shannon-greenlight/Thors-Arsenal/main_board/hardware.kicad_sch

## KiCad design main_board/hardware.kicad_sch (2025-01-23)

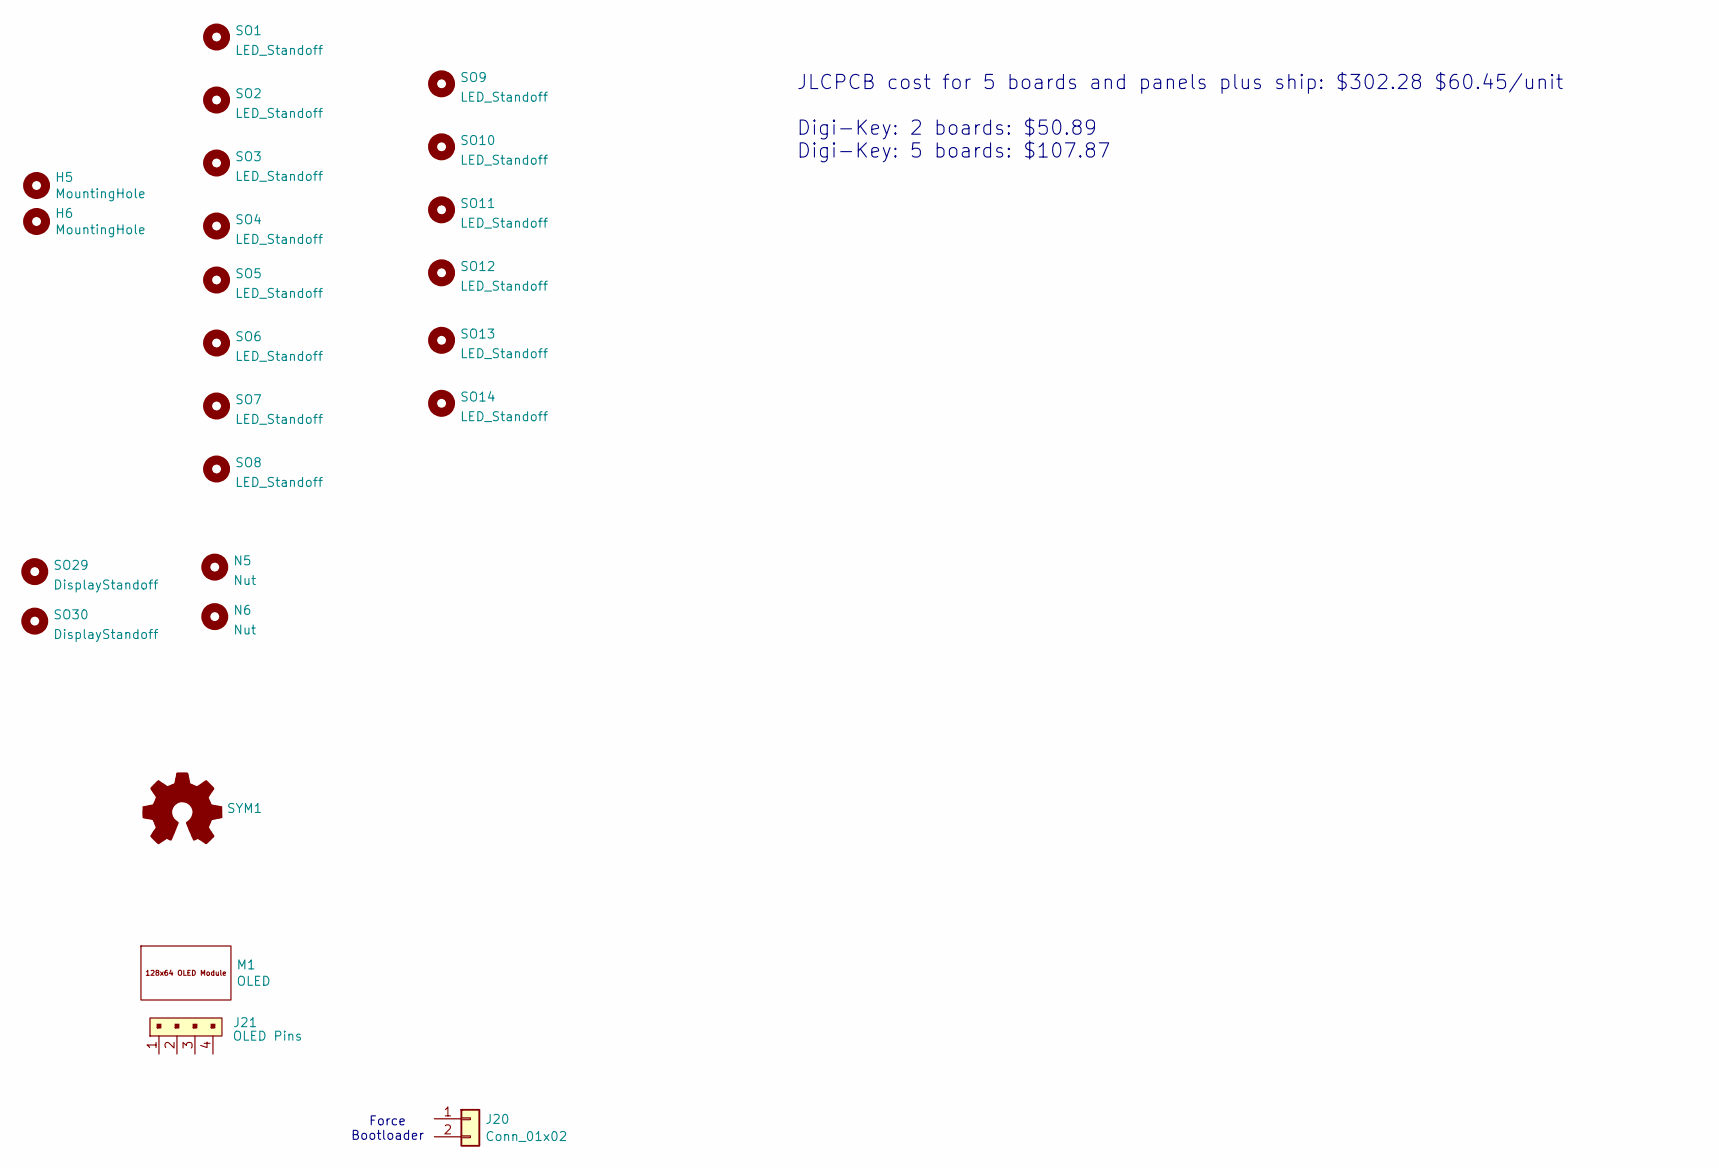
[picture p18: schematic hardware.kicad_sch]

Parts:
H5, H6: MountingHole; MountingHole_2.5mm-No-Margin
J20: Conn_01x02; Digi-Key Part 609-2997-ND
J21: OLED Pins; Digi-Key Part MTLW-104-05-G-S-170-ND
M1: OLED
N5, N6: Nut; Digi-Key Part 36-4687-ND
SO1, SO2, SO3, SO4, SO5, SO6, SO7, SO8, SO9, SO10, SO11, SO12, SO13, SO14: LED_Standoff; Digi-Key Part 732-11594-ND
SO29, SO30: DisplayStandoff; Digi-Key Part 732-13045-ND
SYM1: Logo_Open_Hardware_Small; OSHW-Logo2_7.3x6mm_SilkScreen

Notes on the sheet:
JLCPCB cost for 5 boards and panels plus ship: $302.28 $60.45/unit Digi-Key: 2 boards: $50.89 Digi-Key: 5 boards: $107.87
Force Bootloader
