shannon-greenlight/Thors-Arsenal/main_board/inputs.kicad_sch

## KiCad design main_board/inputs.kicad_sch (2025-01-23)

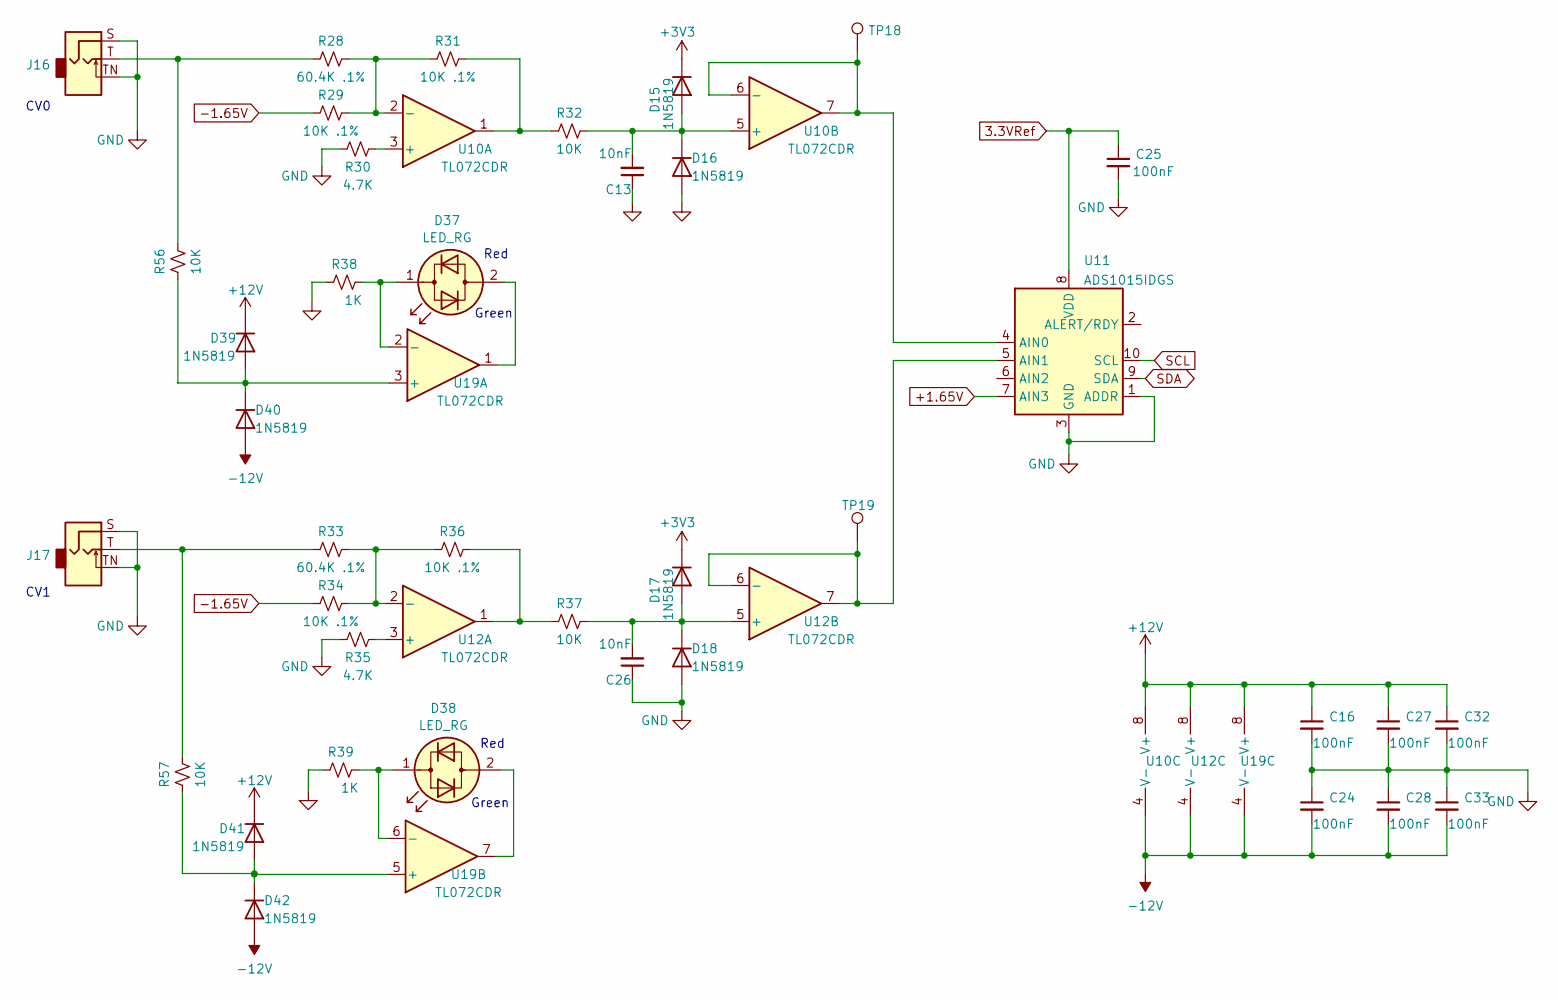
[picture p19: schematic inputs.kicad_sch]

Parts:
C13, C26: 10nF; C_0805_2012Metric_Pad1.18x1.45mm_HandSolder; Digi-Key Part 311-1136-1-ND
C16, C24, C25, C27, C28, C32, C33: 100nF; C_0603_1608Metric; Digi-Key Part 478-10836-1-ND
D15, D16, D17, D18, D39, D40, D41, D42: 1N5819; D_SOD-323; Digi-Key Part 478-7800-1-ND
D37, D38: LED_RG; LED_D3.0mm; Digi-Key Part 754-WP937SURKCGKW-ND
J16, J17: 3.5mm Jack; Jack_3.5mm_QingPu_WQP-PJ398SM_Vertical
R28, R33: 60.4K .1%; R_0603_1608Metric; Digi-Key Part P30.1KDACT-ND
R29, R31, R34, R36: 10K .1%; R_0805_2012Metric_Pad1.20x1.40mm_HandSolder; Digi-Key Part P10KDACT-ND
R30, R35: 4.7K; R_0805_2012Metric_Pad1.20x1.40mm_HandSolder; Digi-Key Part RMCF0805FT4K70CT-ND
R32, R37, R56, R57: 10K; R_0805_2012Metric_Pad1.20x1.40mm_HandSolder; Digi-Key Part 13-RC0805JR-1010KLCT-ND
R38, R39: 1K; R_0805_2012Metric_Pad1.20x1.40mm_HandSolder; Digi-Key Part RNCP0805FTD1K00CT-ND
TP18, TP19: TestPoint; TestPoint_Keystone_5000-5004_Miniature; Digi-Key Part 36-5006-ND
U10, U12, U19: TL072CDR; SOIC-8_3.9x4.9mm_P1.27mm; Digi-Key Part 296-1282-1-ND
U11: ADS1015IDGS; TSSOP-10_3x3mm_P0.5mm; LCSC Part # C193969

Connections:
3.3VRef: C25.1, U11.8 (VDD)
+1.65V: U11.7 (AIN3)
+3V3: D15.1 (K), D17.1 (K)
+12V: C16.1, C27.1, C32.1, D39.1 (K), D41.1 (K), U10.8 (V+), U12.8 (V+), U19.8 (V+)
-1.65V: R29.2, R34.2
-12V: C24.2, C28.2, C33.2, D40.2 (A), D42.2 (A), U10.4 (V-), U12.4 (V-), U19.4 (V-)
GND: C13.1, C16.2, C24.1, C25.2, C26.1, C27.2, C28.1, C32.2, C33.1, D16.2 (A), D18.2 (A), J16.S, J16.TN, J17.S, J17.TN, R30.2, R35.2, R38.1, R39.1, U11.1 (ADDR), U11.3 (GND)
unnamed: C13.2, D15.2 (A), D16.1 (K), R32.1, U10.5 (+)
unnamed: C26.2, D17.2 (A), D18.1 (K), R37.1, U12.5 (+)
unnamed: D37.1 (KA), R38.2, U19.2 (-)
unnamed: D37.2 (AK), U19.1
unnamed: D38.1 (KA), R39.2, U19.6 (-)
unnamed: D38.2 (AK), U19.7
unnamed: D39.2 (A), D40.1 (K), R56.2, U19.3 (+)
unnamed: D41.2 (A), D42.1 (K), R57.2, U19.5 (+)
unnamed: J16.T, R28.2, R56.1
unnamed: J17.T, R33.2, R57.1
unnamed: R28.1, R29.1, R31.2, U10.2 (-)
unnamed: R30.1, U10.3 (+)
unnamed: R31.1, R32.2, U10.1
unnamed: R33.1, R34.1, R36.2, U12.2 (-)
unnamed: R35.1, U12.3 (+)
unnamed: R36.1, R37.2, U12.1
unnamed: TP18.1, U10.6 (-), U10.7, U11.4 (AIN0)
unnamed: TP19.1, U11.5 (AIN1), U12.6 (-), U12.7
SCL: U11.10 (SCL)
SDA: U11.9 (SDA)

Notes on the sheet:
CV0
Red
CV1
Green
