shannon-greenlight/Thors-Arsenal/main_board/main_board.kicad_sch

## KiCad design main_board/main_board.kicad_sch (2025-01-23)

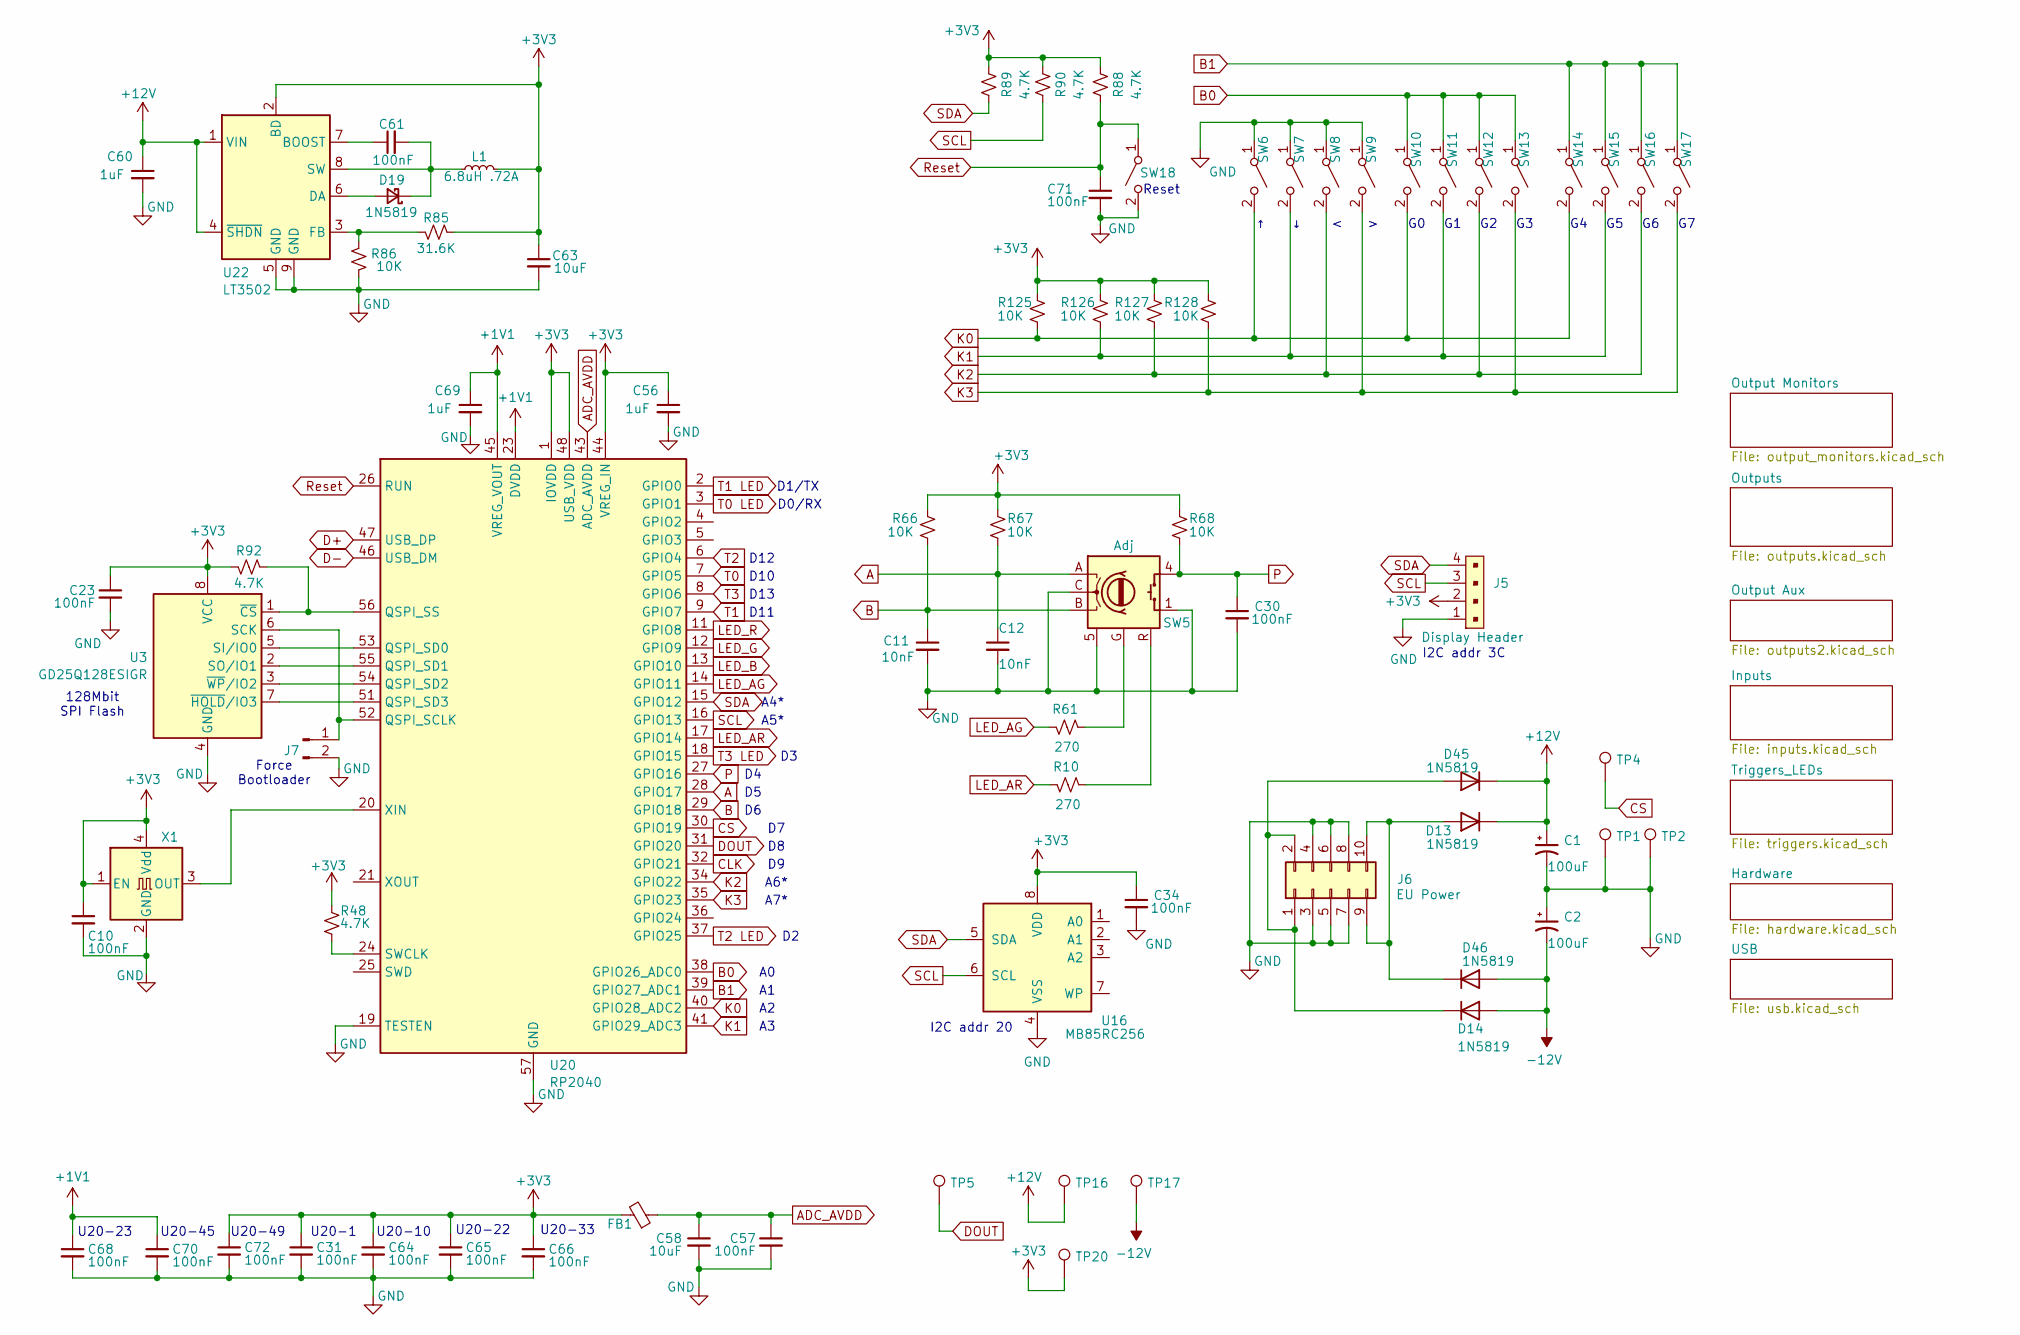
[picture p20: schematic main_board.kicad_sch]

Parts:
C1, C2: 100uF; CP_Elec_6.3x5.4_Nichicon; Digi-Key Part 399-A768EB107M1ELAE036DKR-ND
C10, C23, C30, C31, C34, C57, C61, C64, C65, C66, C68, C70, C71, C72: 100nF; C_0603_1608Metric; Digi-Key Part 478-10836-1-ND
C11, C12: 10nF; C_0805_2012Metric_Pad1.18x1.45mm_HandSolder; Digi-Key Part 311-1136-1-ND
C56, C69: 1uF; C_0603_1608Metric; Digi-Key Part 1276-1029-1-ND
C58, C63: 10uF; C_0603_1608Metric; Digi-Key Part 1276-1029-1-ND
C60: 1uF; C_0805_2012Metric_Pad1.18x1.45mm_HandSolder; Digi-Key Part 1276-1029-1-ND
D13, D14, D19, D45, D46: 1N5819; D_SOD-323; Digi-Key Part 478-7800-1-ND
FB1: BLM18PG471SN1D; L_Murata_BLM18P; LCSC Part # C1002
J5: Display Header; OLED_Header_Slim; MPN 0022232041; Digi-Key Part SAM1087-04-ND
J6: EU Power; PinHeader_2x05_P2.54mm_Vertical; Digi-Key Part S2011EC-05-ND
J7: Conn_01x02_Male; PinHeader_1x02_P2.54mm_Vertical; Digi-Key Part 609-4938-ND
L1: 6.8uH .72A; L_1812_4532Metric; LCSC Part # C703769
R10, R61: 270; R_0603_1608Metric; Digi-Key Part RMCF0603FT23K7CT-ND
R48: 4.7K; R_0603_1608Metric; Digi-Key Part RMCF0805FT4K70CT-ND
R66, R67: 10K; R_0402_1005Metric; Digi-Key Part 13-RC0805JR-1010KLCT-ND
R68, R125, R126, R127, R128: 10K; R_0805_2012Metric_Pad1.20x1.40mm_HandSolder; Digi-Key Part 13-RC0805JR-1010KLCT-ND
R85: 31.6K; R_0603_1608Metric; Digi-Key Part RMCF0603FT23K7CT-ND
R86: 10K; R_0402_1005Metric; Digi-Key Part RMCF0603FT23K7CT-ND
R88, R89, R90, R92: 4.7K; R_0805_2012Metric_Pad1.20x1.40mm_HandSolder; Digi-Key Part RMCF0805FT4K70CT-ND
SW5: Adj; RotaryEncoder_MERP12_24; Digi-Key Part 3746-MERP12-24225M9GR-ND
SW6, SW7, SW8, SW9, SW10, SW11, SW12, SW13, SW14, SW15, SW16, SW17: Push Button; SW_PUSH_6mm; Digi-Key Part 450-1642-ND
SW18: Red Push Button; SW_PUSH_6mm; Digi-Key Part 2-1825910-8-ND
TP1, TP2, TP16, TP17: TestPoint; TestPoint_Keystone_5005-5009_Compact; Digi-Key Part 36-5006-ND
TP4, TP5, TP20: TestPoint; TestPoint_Keystone_5000-5004_Miniature; Digi-Key Part 36-5002-ND
U3: GD25Q128ESIGR; SOP-8_5.28x5.23mm_P1.27mm; Digi-Key Part 1970-GD25Q128ESIGRCT-ND
U16: MB85RC256; SOIC-8_3.9x4.9mm_P1.27mm; LCSC Part # C47538
U20: RP2040; QFN-56-1EP_7x7mm_P0.4mm_EP3.2x3.2mm; LCSC Part # C2040
U22: LT3502; DFN-8-1EP_2x2mm_P0.5mm_EP0.6x1.2mm; LCSC Part # C461522
X1: AMPMDED-12.0000; Oscillator_SMD2520-4P; LCSC Part # C669073

Connections:
+1V1: C68.1, C69.1, C70.1, U20.23 (DVDD), U20.45 (VREG_VOUT), U20.50 (DVDD)
+3V3: C10.1, C23.1, C31.1, C34.1, C56.1, C63.1, C64.1, C65.1, C66.1, C72.1, FB1.2, J5.2, L1.2, R48.1, R66.1, R67.1, R68.1, R85.1, R88.1, R89.1, R90.1, R92.1, R125.1, R126.1, R127.1, R128.1, TP20.1, U3.8 (VCC), U16.8 (VDD), U20.1 (IOVDD), U20.10 (IOVDD), U20.22 (IOVDD), U20.33 (IOVDD), U20.42 (IOVDD), U20.44 (VREG_IN), U20.48 (USB_VDD), U20.49 (IOVDD), U22.2 (BD), X1.1 (EN), X1.4 (Vdd)
+12V: C1.1, C60.1, D13.1 (K), D45.1 (K), TP16.1, U22.1 (VIN), U22.4 (~SHDN)
-12V: C2.2, D14.2 (A), D46.2 (A), TP17.1
A: C12.1, R67.2, SW5.A, U20.28 (GPIO17)
ADC_AVDD: C57.1, C58.1, FB1.1, U20.43 (ADC_AVDD)
B: C11.1, R66.2, SW5.B, U20.29 (GPIO18)
B0: SW10.1 (A), SW11.1 (A), SW12.1 (A), SW13.1 (A), U20.38 (GPIO26_ADC0)
B1: SW14.1 (A), SW15.1 (A), SW16.1 (A), SW17.1 (A), U20.39 (GPIO27_ADC1)
CLK: U20.32 (GPIO21)
CS: TP4.1, U20.30 (GPIO19)
D+: U20.47 (USB_DP)
D-: U20.46 (USB_DM)
DOUT: TP5.1, U20.31 (GPIO20)
GND: C1.2, C2.1, C10.2, C11.2, C12.2, C23.2, C30.2, C31.2, C34.2, C56.2, C57.2, C58.2, C60.2, C63.2, C64.2, C65.2, C66.2, C68.2, C69.2, C70.2, C71.2, C72.2, J5.1, J6.3, J6.4, J6.5, J6.6, J6.7, J6.8, J7.2, R86.1, SW5.1 (S2), SW5.5 (GND), SW5.C, SW6.1 (A), SW7.1 (A), SW8.1 (A), SW9.1 (A), SW18.2 (B), TP1.1, TP2.1, U3.4 (GND), U16.4 (VSS), U20.19 (TESTEN), U20.57 (GND), U22.5 (GND), U22.9 (GND), X1.2 (GND)
K0: R125.2, SW6.2 (B), SW10.2 (B), SW14.2 (B), U20.40 (GPIO28_ADC2)
K1: R126.2, SW7.2 (B), SW11.2 (B), SW15.2 (B), U20.41 (GPIO29_ADC3)
K2: R127.2, SW8.2 (B), SW12.2 (B), SW16.2 (B), U20.34 (GPIO22)
K3: R128.2, SW9.2 (B), SW13.2 (B), SW17.2 (B), U20.35 (GPIO23)
LED_AG: R61.2, U20.14 (GPIO11)
LED_AR: R10.2, U20.17 (GPIO14)
LED_B: U20.13 (GPIO10)
LED_G: U20.12 (GPIO9)
LED_R: U20.11 (GPIO8)
unnamed: C61.1, U22.7 (BOOST)
unnamed: C61.2, D19.1 (K), L1.1, U22.8 (SW)
unnamed: D13.2 (A), D46.1 (K), J6.9, J6.10
unnamed: D14.1 (K), D45.2 (A), J6.1, J6.2
unnamed: D19.2 (A), U22.6 (DA)
unnamed: J7.1, U3.6 (SCK), U20.52 (QSPI_SCLK)
unnamed: R10.1, SW5.R
unnamed: R48.2, U20.24 (SWCLK)
unnamed: R61.1, SW5.G
unnamed: R85.2, R86.2, U22.3 (FB)
unnamed: R92.2, U3.1 (~CS), U20.56 (QSPI_SS)
unnamed: U20.20 (XIN), X1.3 (OUT)
unnamed: U3.7 (~HOLD/IO3), U20.51 (QSPI_SD3)
unnamed: U3.5 (SI/IO0), U20.53 (QSPI_SD0)
unnamed: U3.3 (~WP/IO2), U20.54 (QSPI_SD2)
unnamed: U3.2 (SO/IO1), U20.55 (QSPI_SD1)
P: C30.1, R68.2, SW5.4 (S1), U20.27 (GPIO16)
Reset: C71.1, R88.2, SW18.1 (A), U20.26 (RUN)
SCL: J5.3, R90.2, U16.6 (SCL), U20.16 (GPIO13)
SDA: J5.4, R89.2, U16.5 (SDA), U20.15 (GPIO12)
T0: U20.7 (GPIO5)
T0 LED: U20.3 (GPIO1)
T1: U20.9 (GPIO7)
T1 LED: U20.2 (GPIO0)
T2: U20.6 (GPIO4)
T2 LED: U20.37 (GPIO25)
T3: U20.8 (GPIO6)
T3 LED: U20.18 (GPIO15)

Notes on the sheet:
A5*
A6*
D12
D1/TX
A7*
128Mbit SPI Flash
Force Bootloader
U20-33
U20-23
A4*
D13
I2C addr 3C
D11
U20-45
U20-10
Reset
U20-49
D10
I2C addr 20
U20-1
D0/RX
U20-22
