shannon-greenlight/Thors-Arsenal/main_board/output_monitors.kicad_sch

## KiCad design main_board/output_monitors.kicad_sch (2025-01-20)

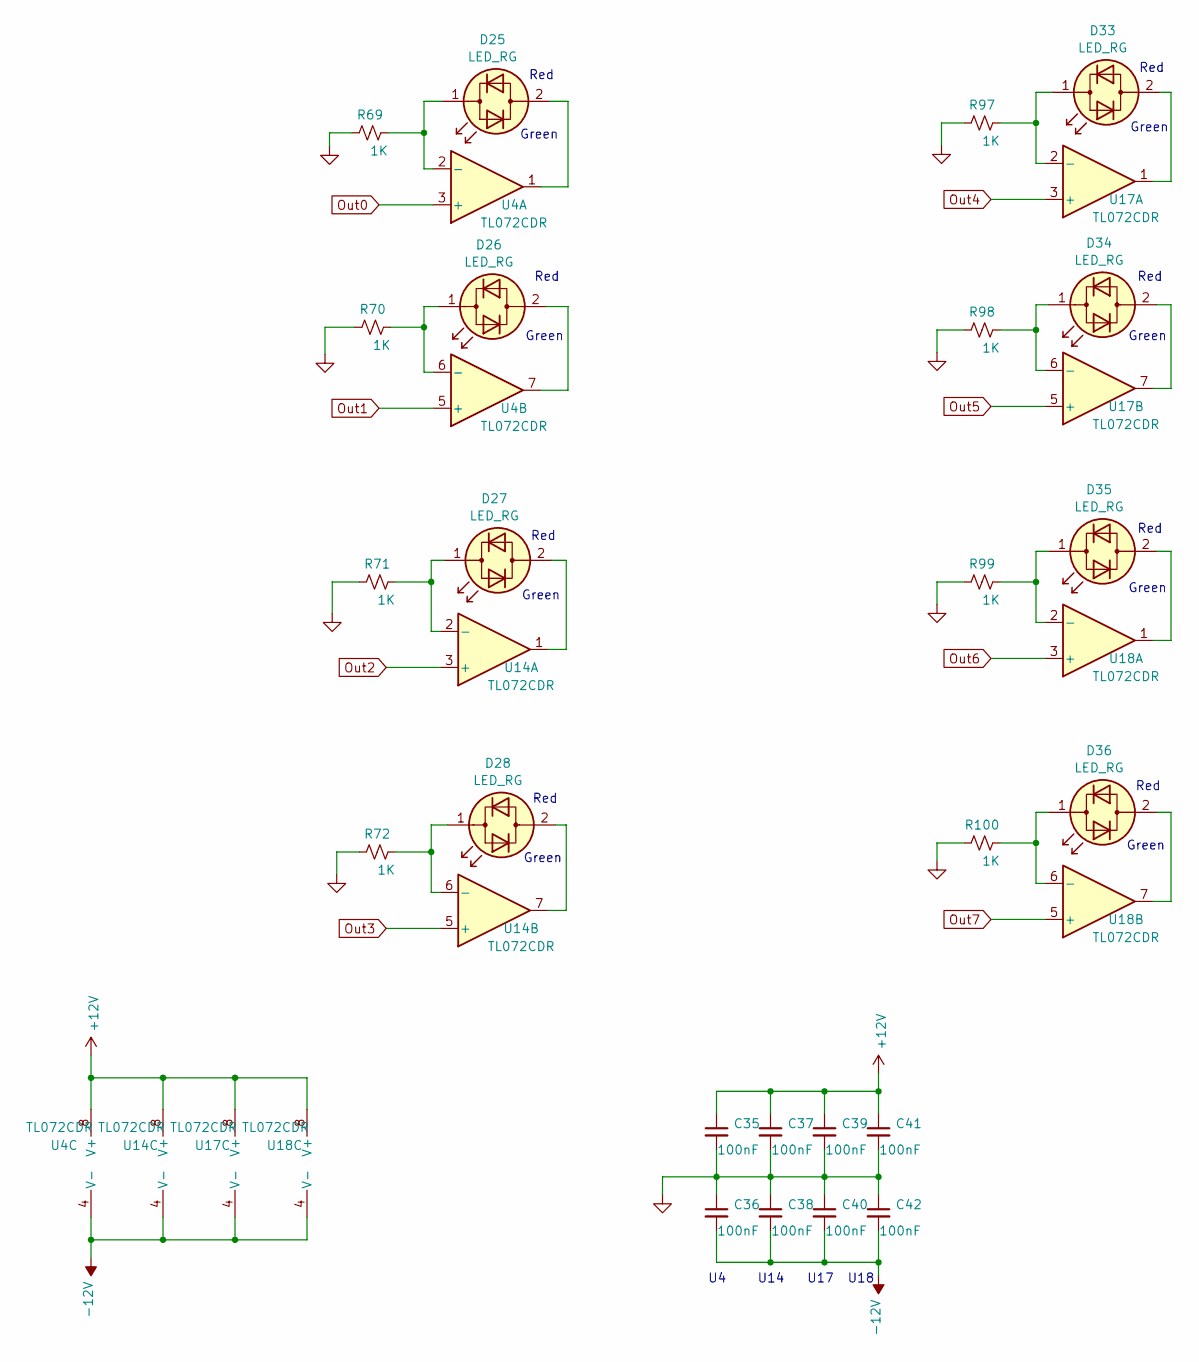
[picture p21: schematic output_monitors.kicad_sch]

Parts:
C35, C36, C37, C38, C39, C40, C41, C42: 100nF; C_0603_1608Metric; Digi-Key Part 478-10836-1-ND
D25, D26, D27, D28, D33, D34, D35, D36: LED_RG; LED_D3.0mm; Digi-Key Part 754-WP937SURKCGKW-ND
R69, R70, R71, R72, R97, R98, R99, R100: 1K; R_0805_2012Metric_Pad1.20x1.40mm_HandSolder; Digi-Key Part RNCP0805FTD1K00CT-ND
U4, U14, U17, U18: TL072CDR; SOIC-8_3.9x4.9mm_P1.27mm; Digi-Key Part 296-1282-1-ND

Connections:
+12V: C35.1, C37.1, C39.1, C41.1, U4.8 (V+), U14.8 (V+), U17.8 (V+), U18.8 (V+)
-12V: C36.2, C38.2, C40.2, C42.2, U4.4 (V-), U14.4 (V-), U17.4 (V-), U18.4 (V-)
GND: C35.2, C36.1, C37.2, C38.1, C39.2, C40.1, C41.2, C42.1, R69.1, R70.1, R71.1, R72.1, R97.1, R98.1, R99.1, R100.1
unnamed: D25.1 (KA), R69.2, U4.2 (-)
unnamed: D25.2 (AK), U4.1
unnamed: D26.1 (KA), R70.2, U4.6 (-)
unnamed: D26.2 (AK), U4.7
unnamed: D27.1 (KA), R71.2, U14.2 (-)
unnamed: D27.2 (AK), U14.1
unnamed: D28.1 (KA), R72.2, U14.6 (-)
unnamed: D28.2 (AK), U14.7
unnamed: D33.1 (KA), R97.2, U17.2 (-)
unnamed: D33.2 (AK), U17.1
unnamed: D34.1 (KA), R98.2, U17.6 (-)
unnamed: D34.2 (AK), U17.7
unnamed: D35.1 (KA), R99.2, U18.2 (-)
unnamed: D35.2 (AK), U18.1
unnamed: D36.1 (KA), R100.2, U18.6 (-)
unnamed: D36.2 (AK), U18.7
Out0: U4.3 (+)
Out1: U4.5 (+)
Out2: U14.3 (+)
Out3: U14.5 (+)
Out4: U17.3 (+)
Out5: U17.5 (+)
Out6: U18.3 (+)
Out7: U18.5 (+)

Notes on the sheet:
Red
Green
U14
U18
U17
