shannon-greenlight/Thors-Arsenal/main_board/outputs2.kicad_sch

## KiCad design main_board/outputs2.kicad_sch (2025-01-23)

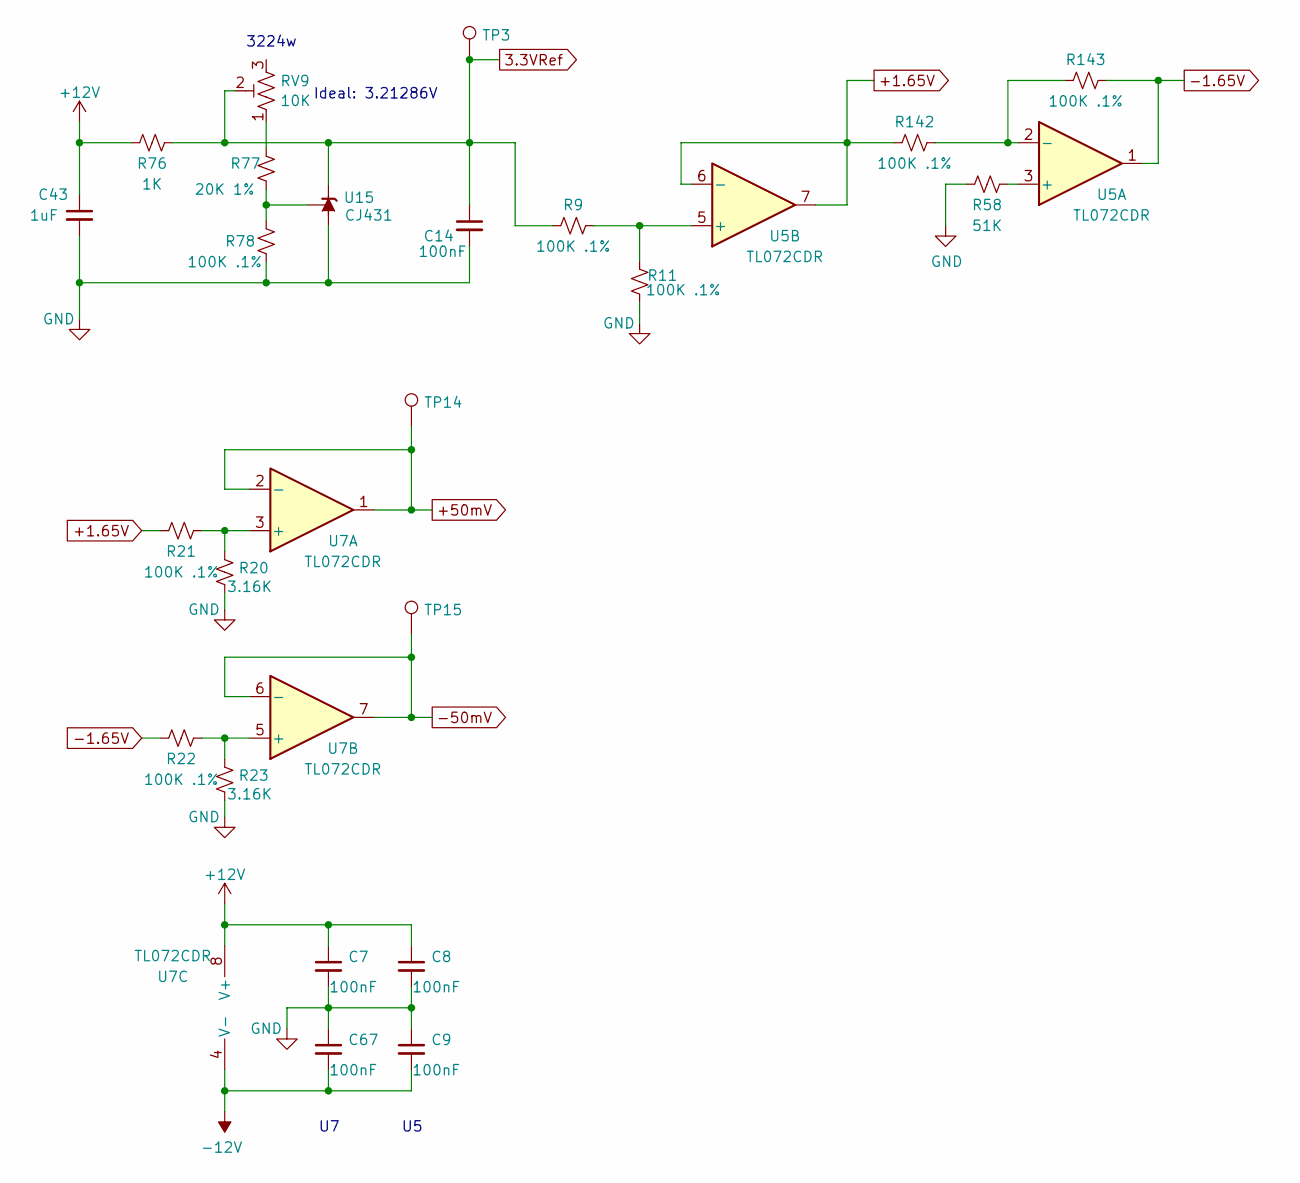
[picture p22: schematic outputs2.kicad_sch]

Parts:
C7, C8, C9, C14, C67: 100nF; C_0603_1608Metric; Digi-Key Part 478-10836-1-ND
C43: 1uF; C_0805_2012Metric_Pad1.18x1.45mm_HandSolder; Digi-Key Part 1276-1029-1-ND
R9, R11, R78, R142, R143: 100K .1%; R_0603_1608Metric; Digi-Key Part YAG1759CT-ND
R20, R23: 3.16K; R_0603_1608Metric; LCSC Part # C22993
R21, R22: 100K .1%; R_0603_1608Metric; Digi-Key Part RNCP0603FTD1K00CT-ND
R58: 51K; R_0603_1608Metric; Digi-Key Part RMCF0805JT33K0CT-ND
R76: 1K; R_0603_1608Metric; Digi-Key Part RNCP0603FTD1K00CT-ND
R77: 20K 1%; R_0603_1608Metric; Digi-Key Part RMCF0603FT23K7CT-ND
RV9: 10K; Potentiometer_Bourns_3224W_Vertical; LCSC Part # C81348
TP3, TP14, TP15: TestPoint; TestPoint_Keystone_5000-5004_Miniature; Digi-Key Part 36-5002-ND
U5, U7: TL072CDR; SOIC-8_3.9x4.9mm_P1.27mm; Digi-Key Part 296-1282-1-ND
U15: CJ431; SOT-23; Digi-Key Part AS431HANTR-G1DICT-ND

Connections:
3.3VRef: C14.1, R9.2, R76.1, RV9.2, TP3.1, U15.2 (K)
+1.65V: R21.2, R142.2, U5.6 (-), U5.7
+12V: C7.1, C8.1, C43.1, R76.2, U7.8 (V+)
+50mV: TP14.1, U7.1, U7.2 (-)
-1.65V: R22.2, R143.1, U5.1
-12V: C9.2, C67.2, U7.4 (V-)
-50mV: TP15.1, U7.6 (-), U7.7
GND: C7.2, C8.2, C9.1, C14.2, C43.2, C67.1, R11.2, R20.2, R23.2, R58.2, R78.2, U15.3 (A)
unnamed: R9.1, R11.1, U5.5 (+)
unnamed: R20.1, R21.1, U7.3 (+)
unnamed: R22.1, R23.1, U7.5 (+)
unnamed: R58.1, U5.3 (+)
unnamed: R77.1, R78.1, U15.1 (REF)
unnamed: R77.2, RV9.1
unnamed: R142.1, R143.2, U5.2 (-)

Notes on the sheet:
Ideal: 3.21286V
3224w
