shannon-greenlight/Thors-Arsenal/main_board/outputs.kicad_sch

## KiCad design main_board/outputs.kicad_sch (2025-01-27, an earlier design)

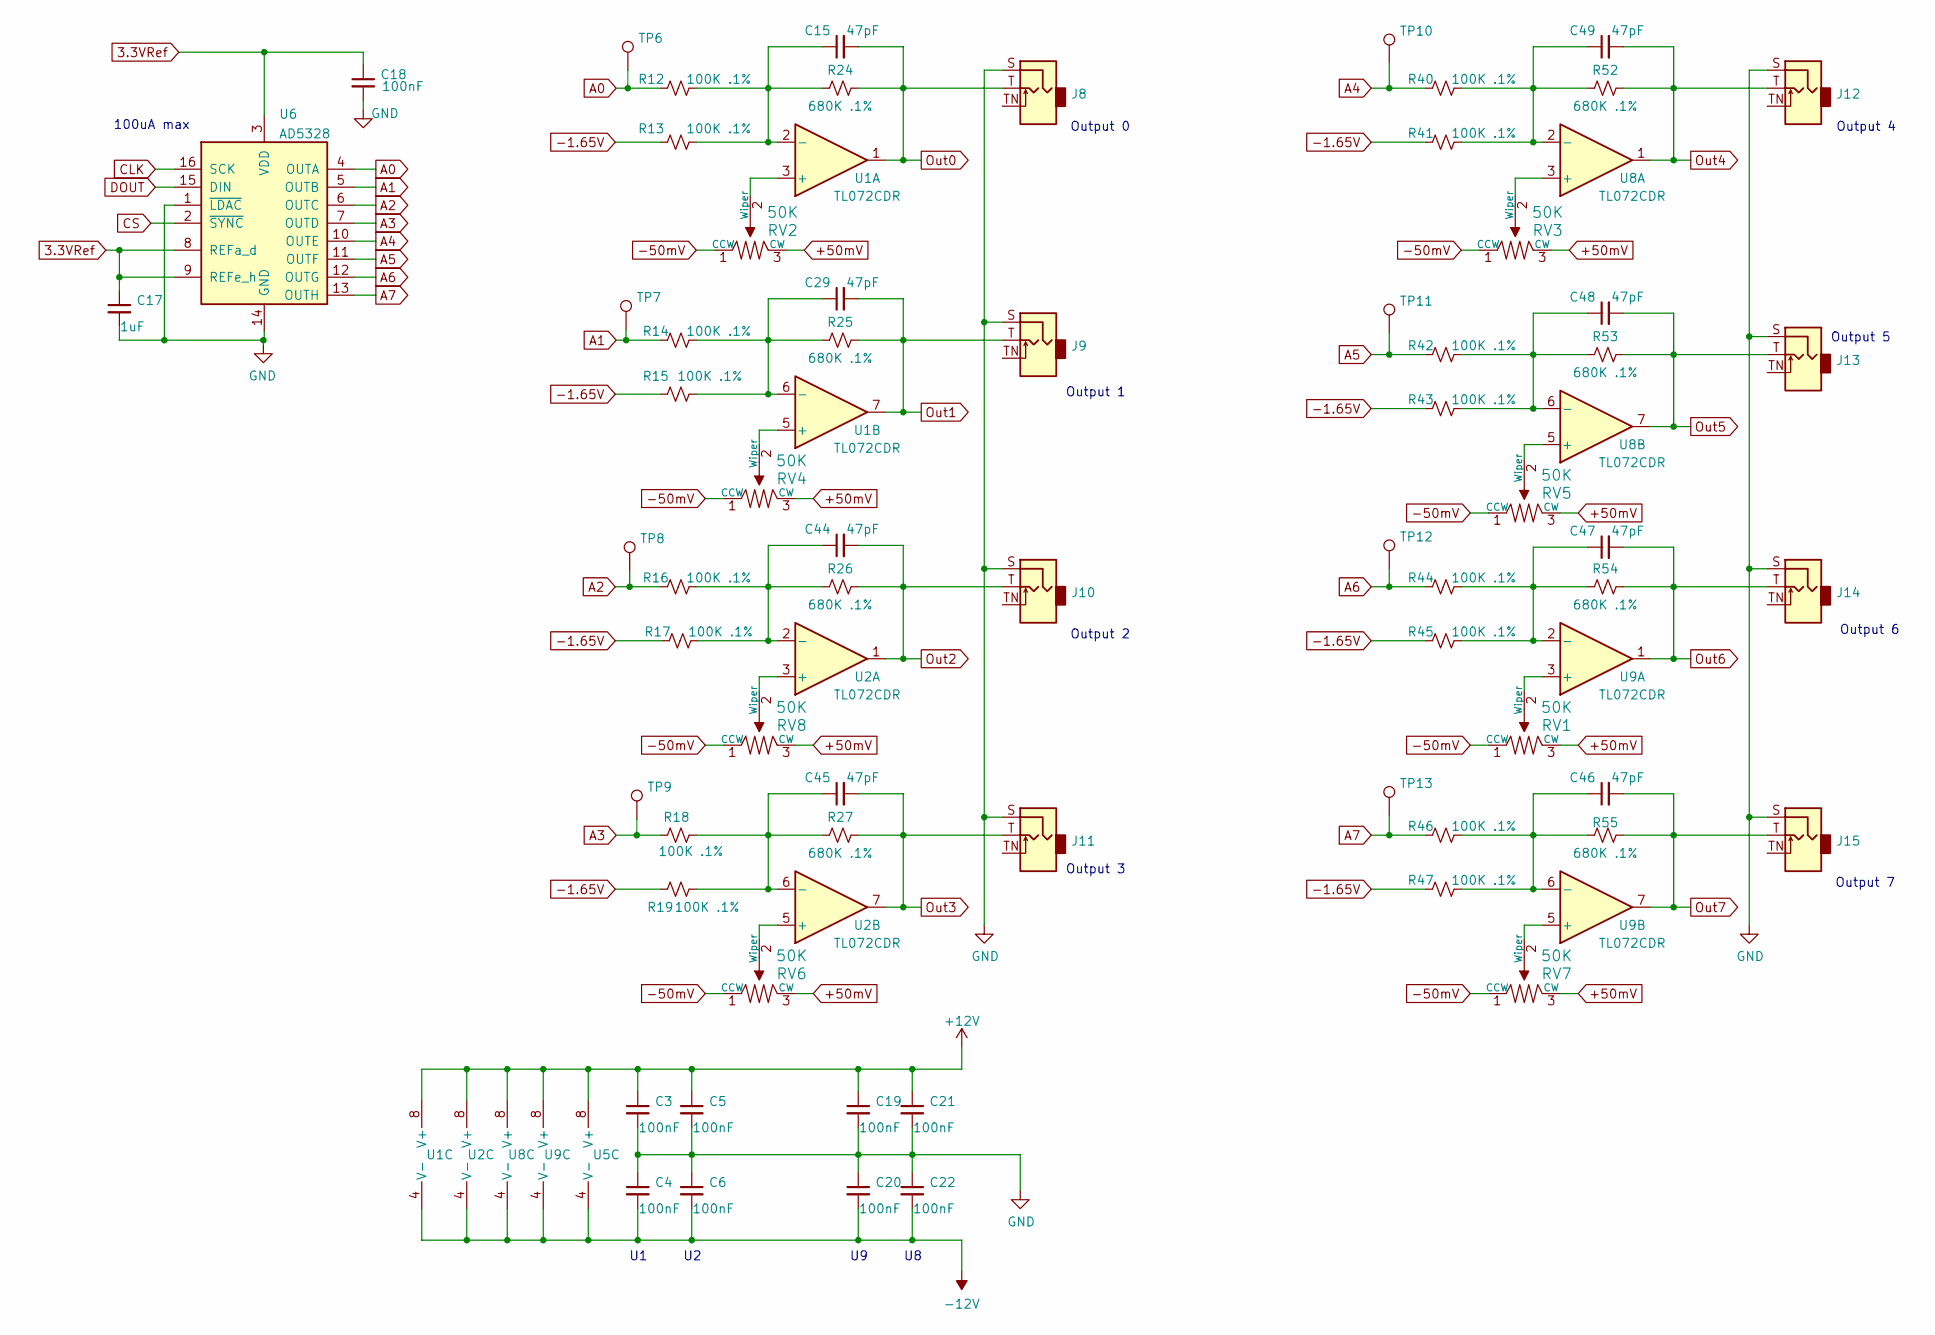
[picture p23: schematic outputs.kicad_sch]

Parts:
C3, C4, C5, C6, C18, C19, C20, C21, C22: 100nF; C_0603_1608Metric; Digi-Key Part 478-10836-1-ND
C15, C29, C44, C45, C46, C47, C48, C49: 47pF; C_0603_1608Metric; Digi-Key Part 1276-1037-1-ND
C17: 1uF; C_0603_1608Metric; Digi-Key Part 478-10836-1-ND
J8, J9, J10, J11, J12, J13, J14, J15: 3.5mm Jack; Jack_3.5mm_QingPu_WQP-PJ398SM_Vertical
R12, R13, R14, R15, R16, R17, R18, R19, R40, R41, R42, R43, R44, R45, R46, R47: 100K .1%; R_0603_1608Metric; Digi-Key Part YAG1759CT-ND
R24, R25, R26, R27, R52, R53, R54, R55: 680K .1%; R_0603_1608Metric; Digi-Key Part P332KDACT-ND
RV1, RV2, RV3, RV4, RV5, RV6, RV7, RV8: 50K; Trimpot_3.8mmx3.6mm_TC33X-2-103E; MPN TC33X-2-103E; Digi-Key Part 118-TC33X-1-503ECT-ND
TP6, TP7, TP8, TP9, TP10, TP11, TP12, TP13: TestPoint; TestPoint_Pad_1.5x1.5mm
U1, U2, U5, U8, U9: TL072CDR; SOIC-8_3.9x4.9mm_P1.27mm; Digi-Key Part 296-1282-1-ND
U6: AD5328; TSSOP-16_4.4x5mm_P0.65mm; LCSC Part # C29162

Connections:
3.3VRef: C17.1, C18.1, U6.3 (VDD), U6.8 (REFa_d), U6.9 (REFe_h)
+12V: C3.1, C5.1, C19.1, C21.1, U1.8 (V+), U2.8 (V+), U5.8 (V+), U8.8 (V+), U9.8 (V+)
+50mV: RV1.3 (CW), RV2.3 (CW), RV3.3 (CW), RV4.3 (CW), RV5.3 (CW), RV6.3 (CW), RV7.3 (CW), RV8.3 (CW)
-1.65V: R13.2, R15.2, R17.2, R19.2, R41.2, R43.2, R45.2, R47.2
-12V: C4.2, C6.2, C20.2, C22.2, U1.4 (V-), U2.4 (V-), U5.4 (V-), U8.4 (V-), U9.4 (V-)
-50mV: RV1.1 (CCW), RV2.1 (CCW), RV3.1 (CCW), RV4.1 (CCW), RV5.1 (CCW), RV6.1 (CCW), RV7.1 (CCW), RV8.1 (CCW)
A0: R12.2, TP6.1, U6.4 (OUTA)
A1: R14.2, TP7.1, U6.5 (OUTB)
A2: R16.2, TP8.1, U6.6 (OUTC)
A3: R18.2, TP9.1, U6.7 (OUTD)
A4: R40.2, TP10.1, U6.10 (OUTE)
A5: R42.2, TP11.1, U6.11 (OUTF)
A6: R44.2, TP12.1, U6.12 (OUTG)
A7: R46.2, TP13.1, U6.13 (OUTH)
CLK: U6.16 (SCK)
CS: U6.2 (~SYNC)
DOUT: U6.15 (DIN)
GND: C3.2, C4.1, C5.2, C6.1, C17.2, C18.2, C19.2, C20.1, C21.2, C22.1, J8.S, J9.S, J10.S, J11.S, J12.S, J13.S, J14.S, J15.S, U6.1 (~LDAC), U6.14 (GND)
unnamed: C15.1, R12.1, R13.1, R24.2, U1.2 (-)
unnamed: C29.1, R14.1, R15.1, R25.2, U1.6 (-)
unnamed: C44.1, R16.1, R17.1, R26.2, U2.2 (-)
unnamed: C45.1, R18.1, R19.1, R27.2, U2.6 (-)
unnamed: C46.1, R46.1, R47.1, R55.2, U9.6 (-)
unnamed: C47.1, R44.1, R45.1, R54.2, U9.2 (-)
unnamed: C48.1, R42.1, R43.1, R53.2, U8.6 (-)
unnamed: C49.1, R40.1, R41.1, R52.2, U8.2 (-)
unnamed: RV1.2 (Wiper), U9.3 (+)
unnamed: RV2.2 (Wiper), U1.3 (+)
unnamed: RV3.2 (Wiper), U8.3 (+)
unnamed: RV4.2 (Wiper), U1.5 (+)
unnamed: RV5.2 (Wiper), U8.5 (+)
unnamed: RV6.2 (Wiper), U2.5 (+)
unnamed: RV7.2 (Wiper), U9.5 (+)
unnamed: RV8.2 (Wiper), U2.3 (+)
Out0: C15.2, J8.T, R24.1, U1.1
Out1: C29.2, J9.T, R25.1, U1.7
Out2: C44.2, J10.T, R26.1, U2.1
Out3: C45.2, J11.T, R27.1, U2.7
Out4: C49.2, J12.T, R52.1, U8.1
Out5: C48.2, J13.T, R53.1, U8.7
Out6: C47.2, J14.T, R54.1, U9.1
Out7: C46.2, J15.T, R55.1, U9.7

Notes on the sheet:
100uA max
Output 3
Output 6
Output 5
Output 1
Output 7
Output 2
Output 0
Output 4
