shannon-greenlight/Thors-Arsenal/main_board/triggers.kicad_sch

## KiCad design main_board/triggers.kicad_sch (2025-01-23)

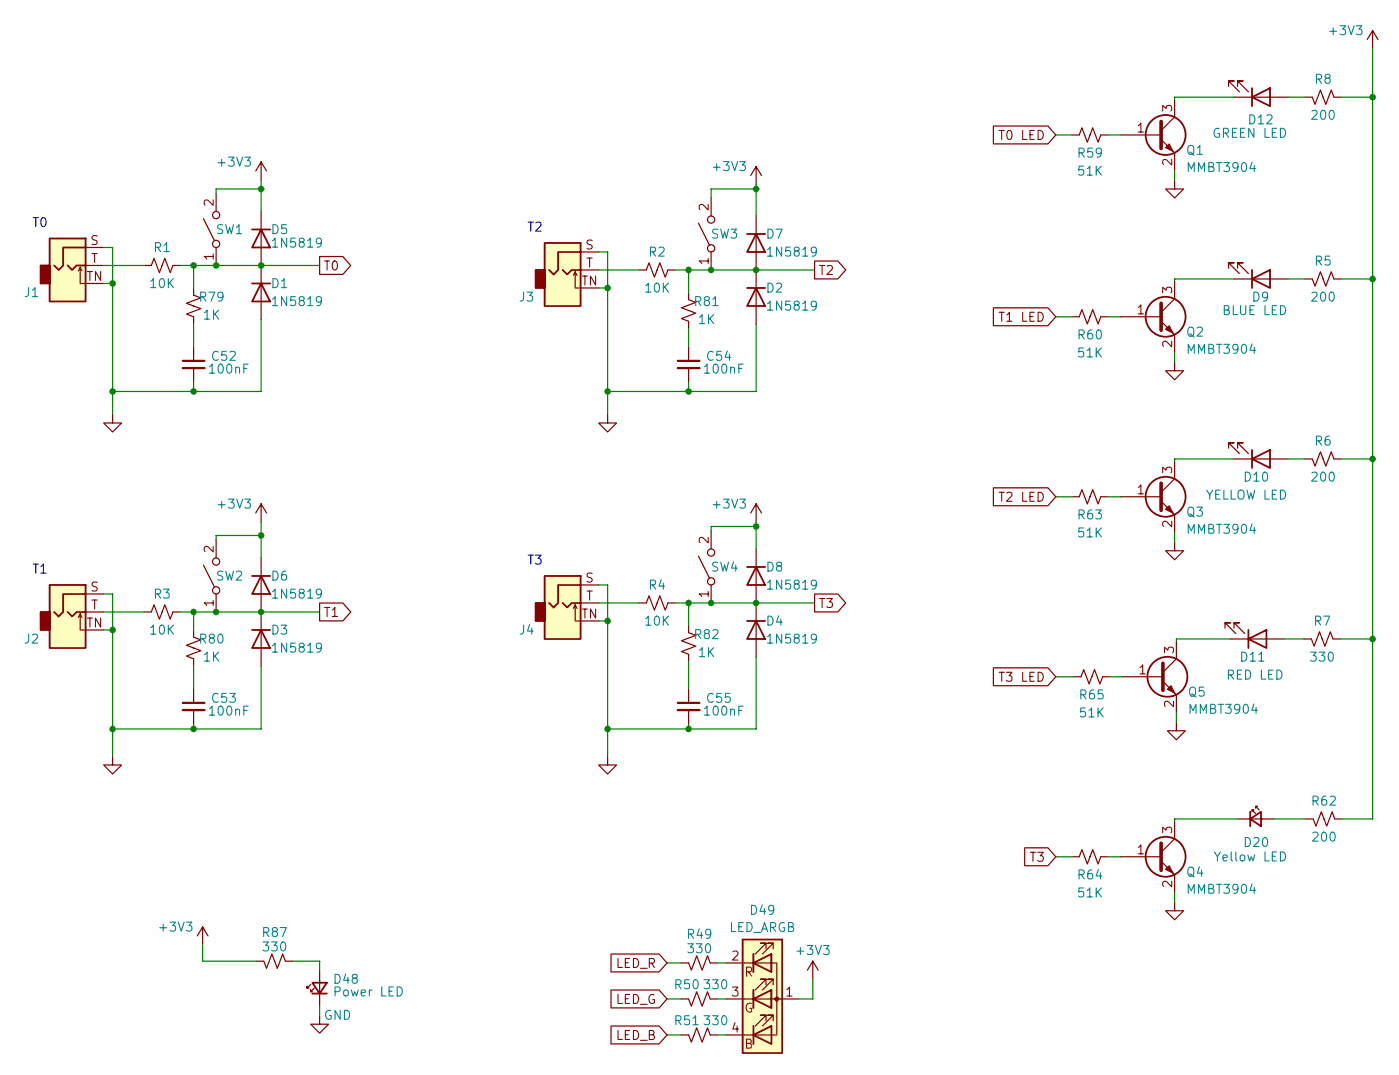
[picture p24: schematic triggers.kicad_sch]

Parts:
C52, C53, C54, C55: 100nF; C_0603_1608Metric; Digi-Key Part 478-10836-1-ND
D1, D2, D3, D4, D5, D6, D7, D8: 1N5819; D_SOD-323; Digi-Key Part 478-7800-1-ND
D9: BLUE LED; LED_D3.0mm; Digi-Key Part 732-11401-ND
D10: YELLOW LED; LED_D3.0mm; Digi-Key Part 732-5010-ND
D11: RED LED; LED_D3.0mm; Digi-Key Part 732-5005-ND
D12: GREEN LED; LED_D3.0mm; Digi-Key Part 732-5007-ND
D20: Yellow LED; LED_0603_1608Metric_Pad1.05x0.95mm_HandSolder; LCSC Part # C72038
D48: Power LED; LED_0603_1608Metric_Pad1.05x0.95mm_HandSolder; LCSC Part # C2290
D49: LED_ARGB; LED_0404; LCSC Part # C158099
J1, J2, J3, J4: 3.5mm Jack; Jack_3.5mm_QingPu_WQP-PJ398SM_Vertical
Q1, Q2, Q3, Q4, Q5: MMBT3904; SOT-23; LCSC Part # C20526
R1, R2, R3, R4: 10K; R_0805_2012Metric_Pad1.20x1.40mm_HandSolder; Digi-Key Part 13-RC0805JR-1010KLCT-ND
R5, R6, R8, R62: 200; R_0603_1608Metric; Digi-Key Part RNCP0805FTD1K00CT-ND
R7: 330; R_0603_1608Metric; Digi-Key Part RNCP0805FTD1K00CT-ND
R49, R50, R51, R87: 330; R_0603_1608Metric; Digi-Key Part RMCF0603FT23K7CT-ND
R59, R60, R63, R64, R65: 51K; R_0603_1608Metric; Digi-Key Part RMCF0805JT33K0CT-ND
R79, R80, R81, R82: 1K; R_0603_1608Metric; Digi-Key Part RNCP0603FTD1K00CT-ND
SW1, SW2, SW3, SW4: Push Button; SW_PUSH_6mm; Digi-Key Part 450-1642-ND

Connections:
+3V3: D5.1 (K), D6.1 (K), D7.1 (K), D8.1 (K), D49.1 (A), R5.1, R6.1, R7.1, R8.1, R62.1, R87.2, SW1.2 (B), SW2.2 (B), SW3.2 (B), SW4.2 (B)
GND: C52.2, C53.2, C54.2, C55.2, D1.2 (A), D2.2 (A), D3.2 (A), D4.2 (A), D48.1 (K), J1.S, J1.TN, J2.S, J2.TN, J3.S, J3.TN, J4.S, J4.TN, Q1.2 (E), Q2.2 (E), Q3.2 (E), Q4.2 (E), Q5.2 (E)
LED_B: R51.2
LED_G: R50.2
LED_R: R49.2
unnamed: C52.1, R79.2
unnamed: C53.1, R80.2
unnamed: C54.1, R81.2
unnamed: C55.1, R82.2
unnamed: D9.1 (K), Q2.3 (C)
unnamed: D9.2 (A), R5.2
unnamed: D10.1 (K), Q3.3 (C)
unnamed: D10.2 (A), R6.2
unnamed: D11.1 (K), Q5.3 (C)
unnamed: D11.2 (A), R7.2
unnamed: D12.1 (K), Q1.3 (C)
unnamed: D12.2 (A), R8.2
unnamed: D20.1 (K), Q4.3 (C)
unnamed: D20.2 (A), R62.2
unnamed: D48.2 (A), R87.1
unnamed: D49.2 (RK), R49.1
unnamed: D49.3 (GK), R50.1
unnamed: D49.4 (BK), R51.1
unnamed: J1.T, R1.2
unnamed: J2.T, R3.2
unnamed: J3.T, R2.2
unnamed: J4.T, R4.2
unnamed: Q1.1 (B), R59.1
unnamed: Q2.1 (B), R60.1
unnamed: Q3.1 (B), R63.1
unnamed: Q4.1 (B), R64.1
unnamed: Q5.1 (B), R65.1
T0: D1.1 (K), D5.2 (A), R1.1, R79.1, SW1.1 (A)
T0 LED: R59.2
T1: D3.1 (K), D6.2 (A), R3.1, R80.1, SW2.1 (A)
T1 LED: R60.2
T2: D2.1 (K), D7.2 (A), R2.1, R81.1, SW3.1 (A)
T2 LED: R63.2
T3: D4.1 (K), D8.2 (A), R4.1, R64.2, R82.1, SW4.1 (A)
T3 LED: R65.2
