shannon-greenlight/Thors-Arsenal/main_board/usb.kicad_sch

## KiCad design main_board/usb.kicad_sch (2025-01-23)

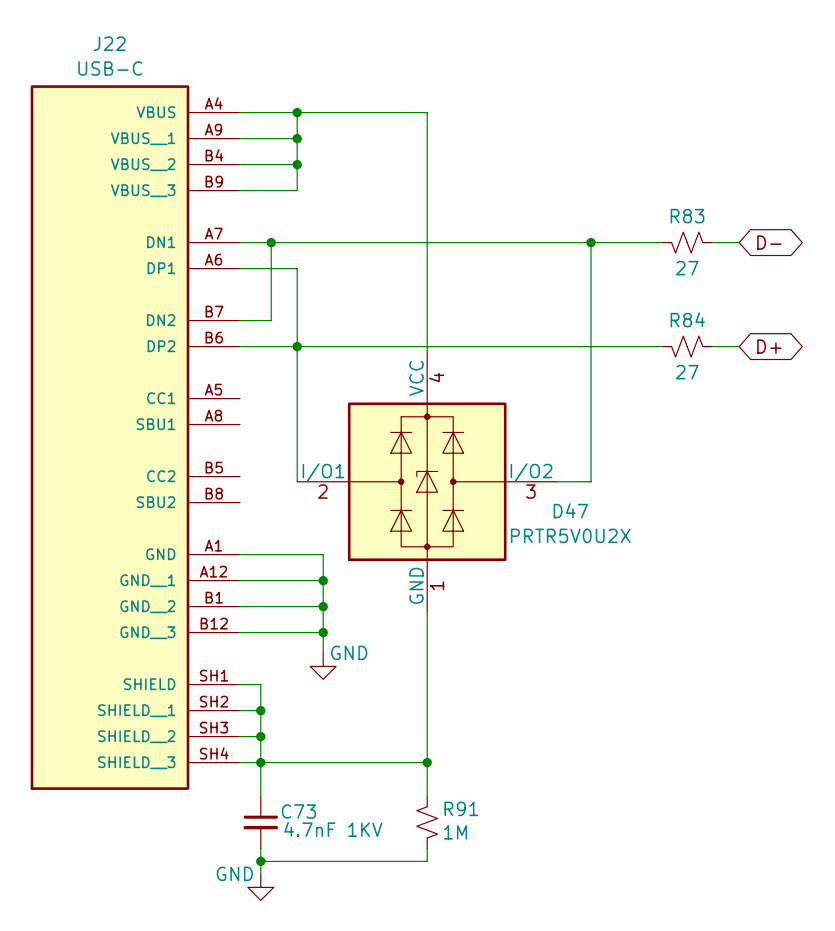
[picture p25: schematic usb.kicad_sch]

Parts:
C73: 4.7nF 1KV; C_0805_2012Metric; Digi-Key Part 1276-1029-1-ND
D47: PRTR5V0U2X; SOT-143; LCSC Part # C12333
J22: USB-C; CUI_UJ20-C-V-C-3-SMT-TR; PARTREV 1.0; Digi-Key Part 2223-UJ20-C-V-C-3-SMT-TRCT-ND
R83, R84: 27; R_0805_2012Metric_Pad1.20x1.40mm_HandSolder; LCSC Part # C17594
R91: 1M; R_0603_1608Metric; LCSC Part # C22935

Connections:
D+: R84.1
D-: R83.1
GND: C73.2, J22.A1 (GND), J22.A12 (GND__1), J22.B1 (GND__2), J22.B12 (GND__3), R91.2
unnamed: C73.1, D47.1 (GND), J22.SH1 (SHIELD), J22.SH2 (SHIELD__1), J22.SH3 (SHIELD__2), J22.SH4 (SHIELD__3), R91.1
unnamed: D47.2 (I/O1), J22.A6 (DP1), J22.B6 (DP2), R84.2
unnamed: D47.3 (I/O2), J22.A7 (DN1), J22.B7 (DN2), R83.2
unnamed: D47.4 (VCC), J22.A4 (VBUS), J22.A9 (VBUS__1), J22.B4 (VBUS__2), J22.B9 (VBUS__3)
