shannon-greenlight/Thors-Arsenal/panel/panel.kicad_sch

## KiCad design panel/panel.kicad_sch (2025-01-20)

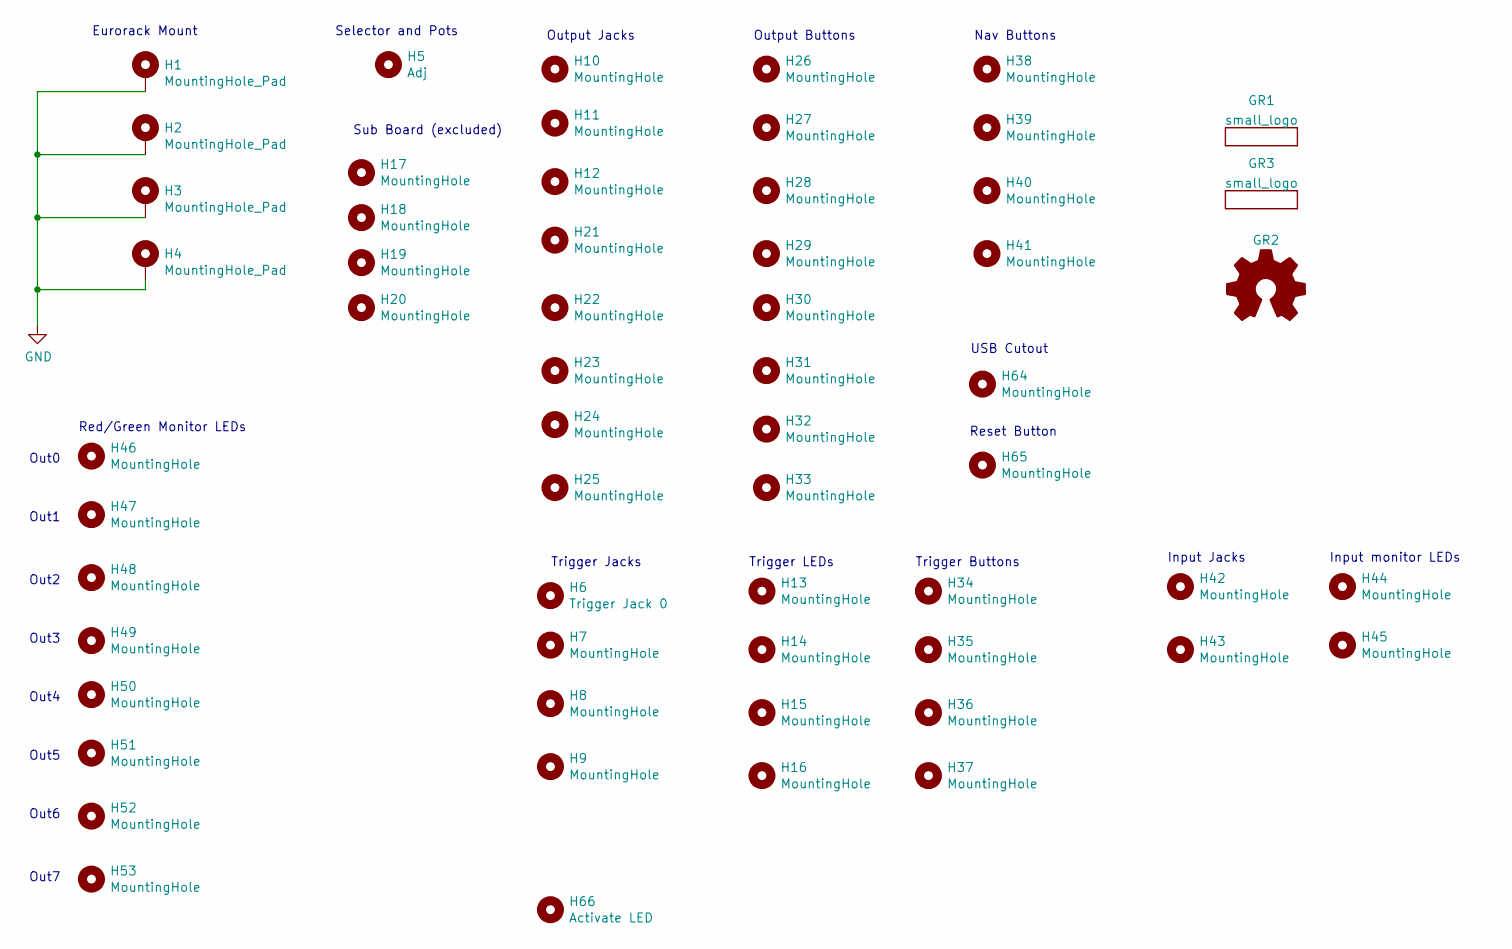
[picture p26: schematic panel.kicad_sch]

Parts:
GR1: small_logo; small_face
GR2: Logo_Open_Hardware_Small; OSHW-Logo_7.5x8mm_SilkScreen
GR3: small_logo; OSHW-Logo_5.7x6mm_SilkScreen
H1, H2, H3, H4: MountingHole_Pad; MountingHole_3.2mm_M3_Slot
H5: Adj; RotaryEncoder_9.0mm
H6: Trigger Jack 0; Jack_3.5mm_QingPu_WQP-PJ398SM_Vertical
H7, H8, H9, H10, H11, H12, H21, H22, H23, H24, H25, H42, H43: MountingHole; Jack_3.5mm_QingPu_WQP-PJ398SM_Vertical
H13, H14, H15, H16: MountingHole; 3mmLED_seethru_small
H17, H18, H19, H20: MountingHole; MountingHole_2.5mm
H26, H27, H28, H29, H30, H31, H32, H33, H34, H35, H36, H37, H38, H39, H40, H41, H65: MountingHole; PushButton3.7mm
H44, H45, H46, H47, H48, H49, H50, H51, H52, H53: MountingHole; 4mmLED_SeeThru
H64: MountingHole; USB_C_Slot_Exact
H66: Activate LED; 3mmLED_seethru_small

Connections:
GND: H1.1, H2.1, H3.1, H4.1

Notes on the sheet:
Out5
Input Jacks
Reset Button
Trigger LEDs
Sub Board (excluded)
USB Cutout
Selector and Pots
Out4
Output Jacks
Input monitor LEDs
Out3
Trigger Jacks
Eurorack Mount
Nav Buttons
Out6
Out2
Output Buttons
Out0
Red/Green Monitor LEDs
Trigger Buttons
Out7
Out1
