shannon-greenlight/Thors-Arsenal/code/src/hardware/greenface/mbed_nano/0.0.0/variants/GREENFACE_RP2040/variant.h

/*
  Copyright (c) 2014-2016 Arduino LLC.  All right reserved.

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
  You should have received a copy of the GNU Lesser General Public
  License along with this library; if not, write to the Free Software
  Foundation, Inc., 51 Franklin St, Fifth Floor, Boston, MA  02110-1301  USA
*/

#ifndef _VARIANT_GREENFACE_RP2040
#define _VARIANT_GREENFACE_RP2040

// #undef LEDR
// #undef LEDG
// #undef LEDB

/*----------------------------------------------------------------------------
 *        Headers
 *----------------------------------------------------------------------------*/

// #include "WVariant.h"
// #include "nina_pins.h"

// #pragma message("Compiling variant.h")

static const uint8_t A4 = 12;
static const uint8_t A5 = 13;
static const uint8_t A6 = 20;
static const uint8_t A7 = 21;

static const uint8_t LEDR = 27;
static const uint8_t LEDG = 28;
static const uint8_t LEDB = 29;
static const uint8_t LEDAG = 30;
static const uint8_t LEDAR = 31;

#endif /* _VARIANT_GREENFACE_RP2040 */
