shannon-greenlight/Thors-Arsenal/code/src/product_defs.h

#ifdef THORS_ARSENAL
#define PRODUCT_NAME "Thor's Arsenal"
#define DEVICE_NAME "Loki"
#elif defined BONKULATOR
#define PRODUCT_NAME "Bonkulator"
#define DEVICE_NAME "Bonky"
#endif

#define NUM_INPUTS 2
#define NUM_OUTPUTS 8
#define WAVEFORM_PARTS 128
